adamforbes92/CAN2RPM/PlatformIO/include/can2rpm_tasks.h

#pragma once

// Starts all background RTOS tasks.
// Call once from setup() after all peripherals are initialised.
void startTasks();

// Temporarily pause/resume output update tasks during manual sweeps.
void suspendOutputTasks();
void resumeOutputTasks();
